Defconbots/2014_target/firmware/src/state.c

/**
@file state.c
@brief Simple state machine handler
@author Joe Brown
*/
#include "global.h"
#include "state.h"

//::::::::::::::::::::::::::::::::::::::::::::::::::::::::::::::::::::::::::::::
//                            __                        __
//                           / /   ____   _____ ____ _ / /
//                          / /   / __ \ / ___// __ `// /
//                         / /___/ /_/ // /__ / /_/ // /
//                        /_____/\____/ \___/ \__,_//_/
//
//::::::::::::::::::::::::::::::::::::::::::::::::::::::::::::::::::::::::::::::
/** @brief Default events not enqueued by users */
enum LocalDefaults {DEFAULT_EVENTS};

//::::::::::::::::::::::::::::::::::::::::::::::::::::::::::::::::::::::::::::::
/**
@brief Dequeue an event from the event queue
@details
Removes an event from the event queue and passes it to the current state.
@param[in] s A pointer to the state machine to dequeue an event from
@return The next event to be processed by the current state
*/
static uint8_t DequeueEvent(StateMachine* s);

/**
@brief Get the next state from the transition table
@details
Get the next state from the transition table based on the current state and the
most recent event dequeued from the event queue.
@param[in] s A pointer to the state machine to look for transitions in
@param[in] event The next event dequeue from the event queue
@return The next state to be run based on transition rules
*/
static State LookupTransition(StateMachine* s, uint8_t event);

//::::::::::::::::::::::::::::::::::::::::::::::::::::::::::::::::::::::::::::::
//                            ____        _  __
//                           /  _/____   (_)/ /_
//                           / / / __ \ / // __/
//                         _/ / / / / // // /_
//                        /___//_/ /_//_/ \__/
//
//::::::::::::::::::::::::::::::::::::::::::::::::::::::::::::::::::::::::::::::
StateMachine StateMachineCreate(const Transition* rules, uint8_t t_size, State state)
{
    StateMachine s;
    s.start = 0;
    s.event_cnt = 0;
    s.transitions = (Transition*)rules;
    s.transition_table_size = (t_size / sizeof(Transition));
    s.state = state;
    StateMachinePublishEvent(&s, ENTER);
    return (s);
}

//::::::::::::::::::::::::::::::::::::::::::::::::::::::::::::::::::::::::::::::
void StateMachinePublishEvent(StateMachine* s, uint8_t event)
{
    if (s->event_cnt < MAX_EVENT_CNT)
    {
        if (s->start + s->event_cnt == MAX_EVENT_CNT)
        {
            s->event_queue[0] = event;
        }
        else
        {
            s->event_queue[s->start + s->event_cnt] = event;
        }
        s->event_cnt++;
    }
}

//::::::::::::::::::::::::::::::::::::::::::::::::::::::::::::::::::::::::::::::
uint8_t DequeueEvent(StateMachine* s)
{
    uint8_t ret = IDLE;
    if (s->event_cnt)
    {
        ret = s->event_queue[s->start];
        if (s->start == MAX_EVENT_CNT - 1)
        {
            s->start = 0;
        }
        else
        {
            s->start += 1;
        }
        s->event_cnt -= 1;
    }
    return ret;
}

//::::::::::::::::::::::::::::::::::::::::::::::::::::::::::::::::::::::::::::::
State LookupTransition(StateMachine* s, uint8_t event)
{
    uint8_t i = 0;
    State ret_state = s->state;

    // if the event is idle or enter/exit just return state)
    if (event != IDLE && event != ENTER && event != EXIT)
    {
        // if event is a new event find the transition
        for (i = 0; i < s->transition_table_size; i++)
        {
            if (s->transitions[i].current_state == s->state &&
                s->transitions[i].event_code    == event)
            {
                ret_state = s->transitions[i].next_state;
                break;
            }
        }
    }
    return ret_state;
}

//::::::::::::::::::::::::::::::::::::::::::::::::::::::::::::::::::::::::::::::
void StateMachineRun(StateMachine* s)
{
    // peek at the next event in the queue
    uint8_t next_event = DequeueEvent(s);
    State next_state = LookupTransition(s, next_event);
    // Will this cause a transition?
    if (s->state != next_state)
    {
        (s->state)(EXIT);
        s->state = next_state;
        (s->state)(ENTER);
    }
    else
    {
        (s->state)(next_event);
    }
}
