Defconbots/2014_target/firmware/juicy.h

/**
@file juicy.h
@brief Definitions for juicy fx
@author Joe Brown
*/
#ifndef JUICY_H
#define JUICY_H

void JuicyBlueOn(void);
void JuicyBlueOff(void);
void JuicyRedOn(void);
void JuicyRedOff(void);
void JuicyBothOn(void);
void JuicyBothOff(void);

#endif
